matthijsberg/SCO2/Pictures/SCO2-sensor-002.jpg

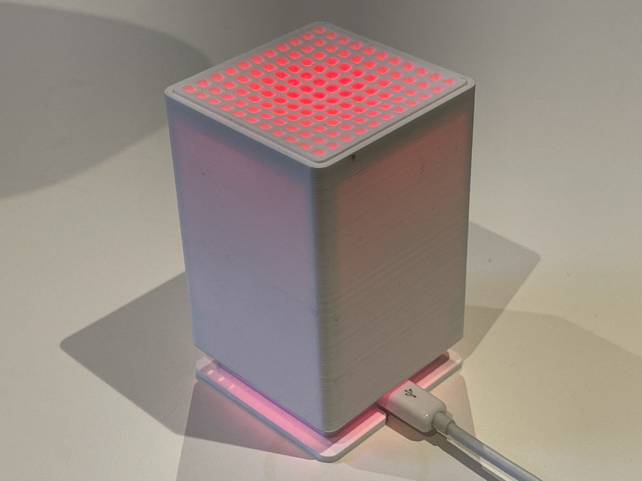
Pictures/SCO2-sensor-002.jpg
